ZSWatch/Watch-HW/production/watch-RELEASED/HTML/images/cat_pdf_drill_map_ZSWatch-Watch-PTH_drill_map.png

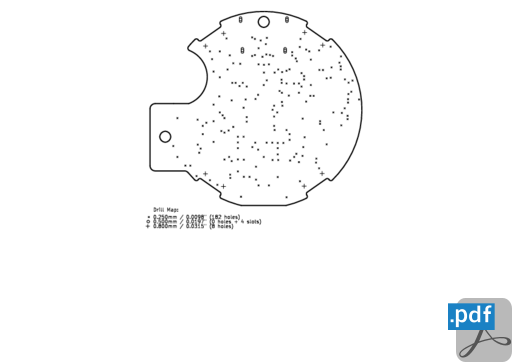
production/watch-RELEASED/HTML/images/cat_pdf_drill_map_ZSWatch-Watch-PTH_drill_map.png
