ZSWatch/Watch-HW/production/watch-RELEASED/HTML/images/cat_png_3d_viewer_bottom_ZSWatch-Watch-bottom.png

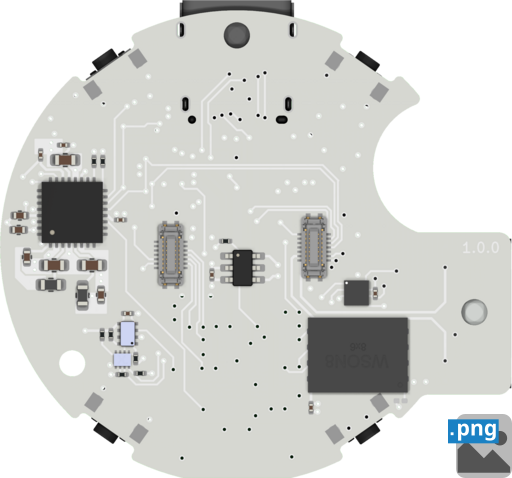
production/watch-RELEASED/HTML/images/cat_png_3d_viewer_bottom_ZSWatch-Watch-bottom.png
