ZSWatch/Watch-HW/production/watch-RELEASED/HTML/images/cat_png_3d_viewer_top_ZSWatch-Watch-top.png

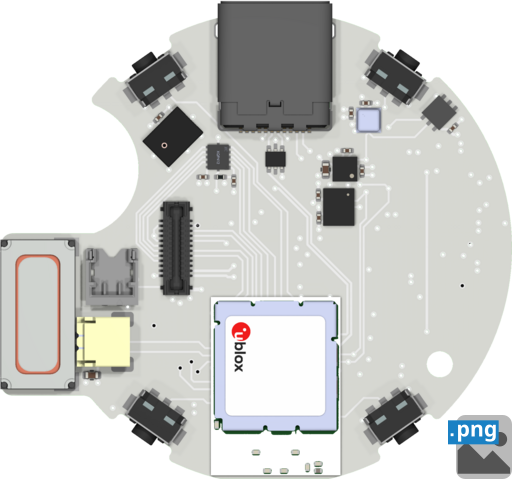
production/watch-RELEASED/HTML/images/cat_png_3d_viewer_top_ZSWatch-Watch-top.png
